Boogs77/BO6502_65C02-based_modular_computer/BO6502 BACKPLATE/README.md

Backplate
==============

Simple blackplate in two different versions. According to requirent 39 pins are used (Address, Data and Power&Signal) with 3 spare connection.

**backplate_final_rev02**

Backplate with 5v 7805 voltage regolator 

5 slots with 39 pins each
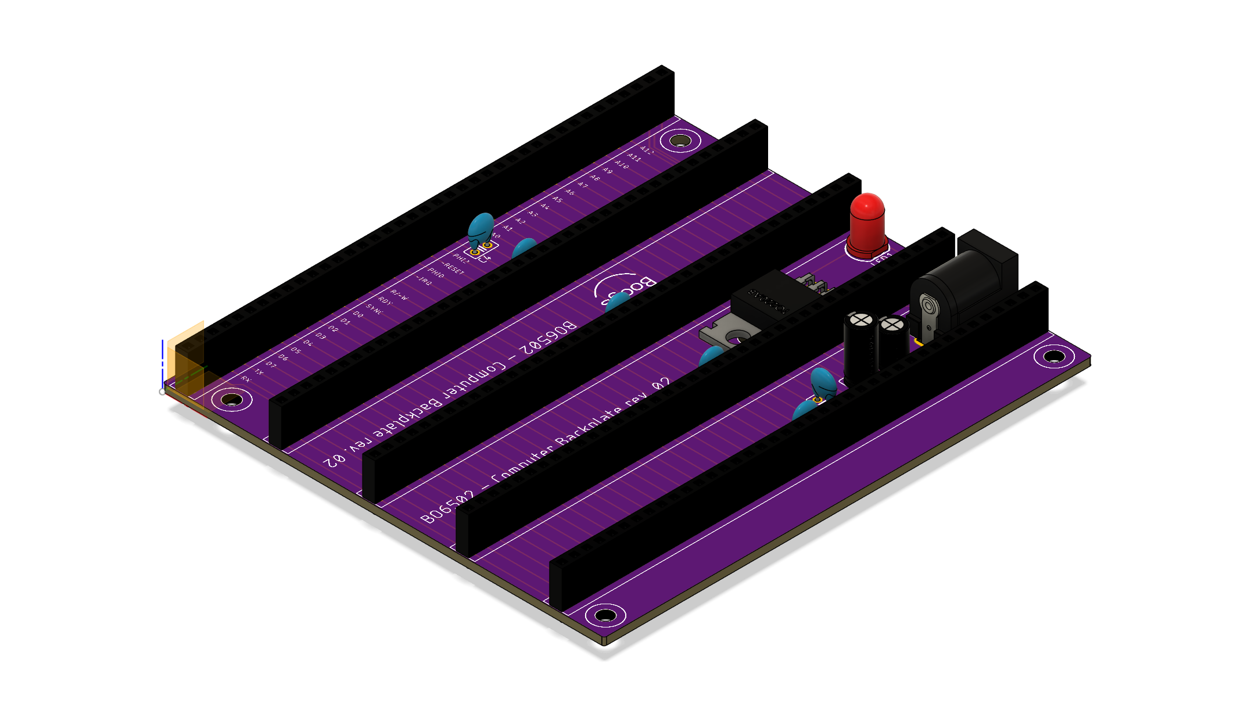
[picture p15: BO6502 BACKPLATE/gallery/backplate_final_rev02.png]


**backplate5V_final_rev01**

Backplate for 5v source  

5 slots with 39 pins each

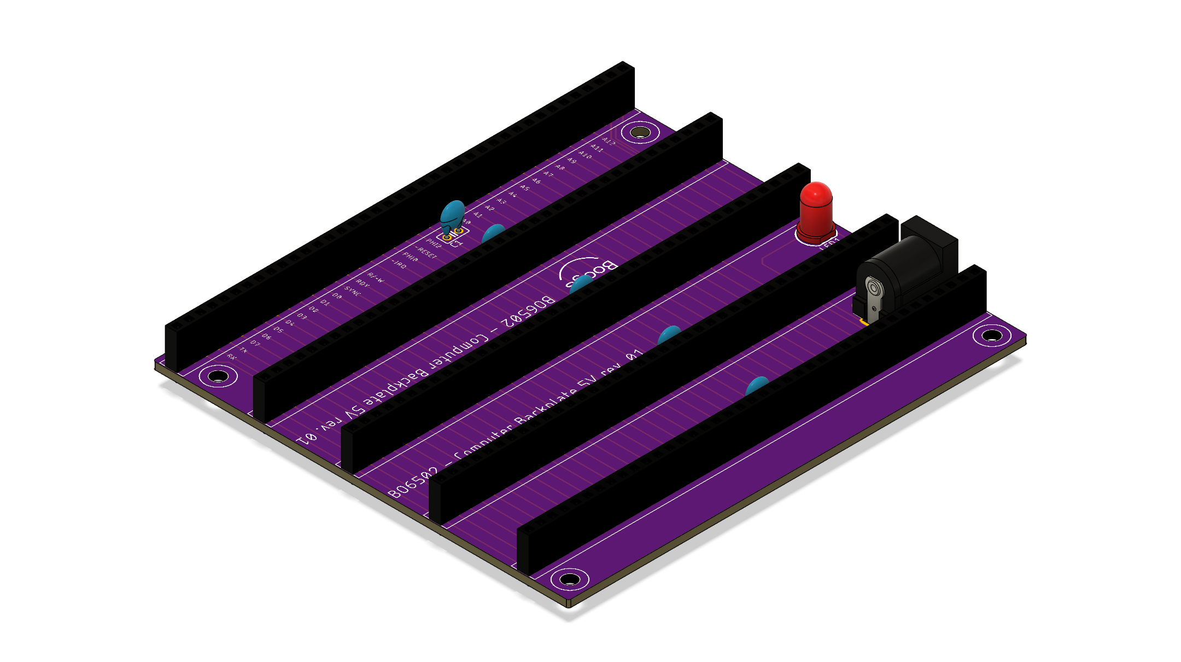
[picture p16: BO6502 BACKPLATE/gallery/backplate5V_final_rev01.png]
