Boogs77/BO6502_65C02-based_modular_computer/BO6502 CPU/eagle/CPU_final_rev02.brd

## EAGLE design BO6502 CPU/eagle/CPU_final_rev02.brd (2026-02-01)

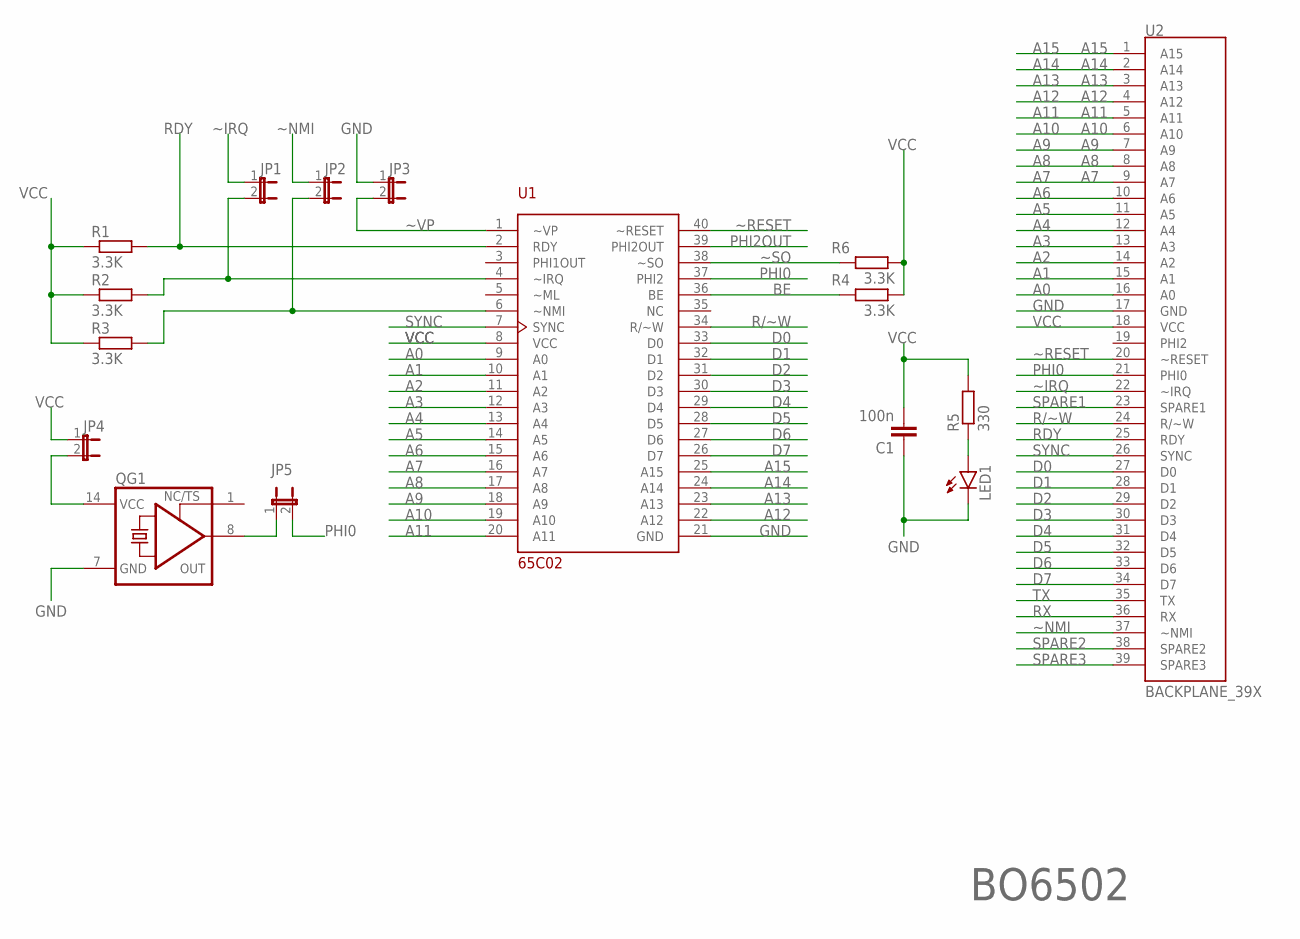
[picture p50: schematic CPU_final_rev02.sch]

Parts:
C1: 100n; C025-025X050
JP1, JP2, JP3, JP4, JP5: JP1E; JP1
LED1: LED5MM
QG1: XO-14; DIL14S
R1, R2, R3, R4, R6: 3.3K; 0207/10
R5: 330; 0207/10
U1: 65C02; DIL40
U2: BACKPLANE_39X; BP_39X

Connections:
A0: U1.9 (A0), U2.16 (A0)
A1: U1.10 (A1), U2.15 (A1)
A2: U1.11 (A2), U2.14 (A2)
A3: U1.12 (A3), U2.13 (A3)
A4: U1.13 (A4), U2.12 (A4)
A5: U1.14 (A5), U2.11 (A5)
A6: U1.15 (A6), U2.10 (A6)
A7: U1.16 (A7), U2.9 (A7)
A8: U1.17 (A8), U2.8 (A8)
A9: U1.18 (A9), U2.7 (A9)
A10: U1.19 (A10), U2.6 (A10)
A11: U1.20 (A11), U2.5 (A11)
A12: U1.22 (A12), U2.4 (A12)
A13: U1.23 (A13), U2.3 (A13)
A14: U1.24 (A14), U2.2 (A14)
A15: U1.25 (A15), U2.1 (A15)
BE: R4.1, U1.36 (BE)
D0: U1.33 (D0), U2.27 (D0)
D1: U1.32 (D1), U2.28 (D1)
D2: U1.31 (D2), U2.29 (D2)
D3: U1.30 (D3), U2.30 (D3)
D4: U1.29 (D4), U2.31 (D4)
D5: U1.28 (D5), U2.32 (D5)
D6: U1.27 (D6), U2.33 (D6)
D7: U1.26 (D7), U2.34 (D7)
GND: C1.1, JP3.1, LED1.K (C), QG1.7 (GND), U1.21 (GND), U2.17 (GND)
unnamed: JP4.2, QG1.14 (VCC)
unnamed: JP1.2, R2.2, U1.4 (~IRQ)
unnamed: JP2.2, R3.2, U1.6 (~NMI)
unnamed: JP5.1, QG1.8 (OUT)
unnamed: LED1.A, R5.1
PHI0: JP5.2, U1.37 (PHI2), U2.21 (PHI0)
PHI2OUT: U1.39 (PHI2OUT)
R/~W: U1.34 (R/~W), U2.24 (R/~W)
RDY: R1.2, U1.2 (RDY), U2.25 (RDY)
RX: U2.36 (RX)
SPARE1: U2.23 (SPARE1)
SPARE2: U2.38 (SPARE2)
SPARE3: U2.39 (SPARE3)
SYNC: U1.7 (SYNC), U2.26 (SYNC)
TX: U2.35 (TX)
VCC: C1.2, JP4.1, R1.1, R2.1, R3.1, R4.2, R5.2, R6.2, U1.8 (VCC), U2.18 (VCC)
~IRQ: JP1.1, U2.22 (~IRQ)
~NMI: JP2.1, U2.37 (~NMI)
~RESET: U1.40 (~RESET), U2.20 (~RESET)
~SO: R6.1, U1.38 (~SO)
~VP: JP3.2, U1.1 (~VP)

Notes on the sheet:
BO6502

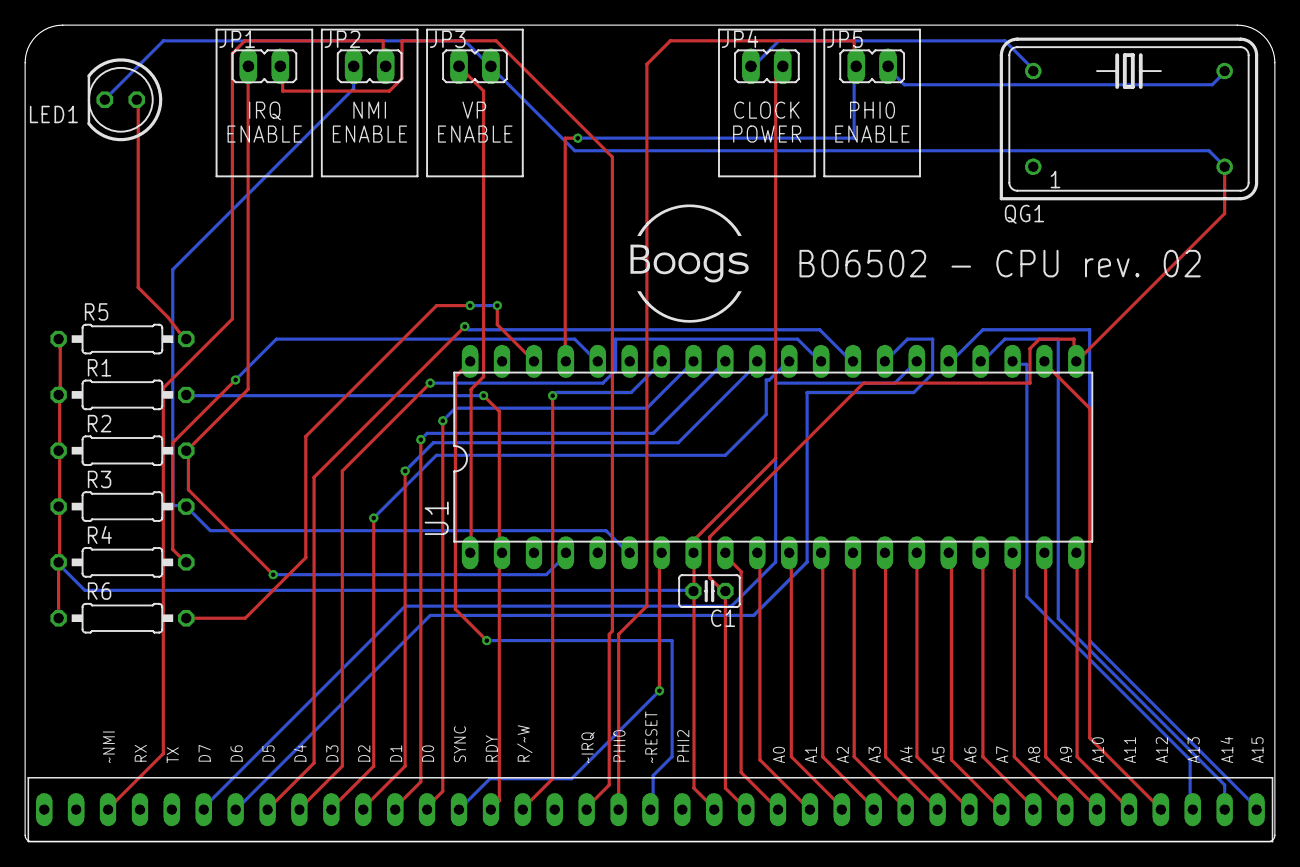
[picture p51: board CPU_final_rev02.brd from above]

Board: 2 copper layers, 99.5 x 65.0 mm, 16 parts (0 on the bottom side), 41 nets.
