Boogs77/BO6502_65C02-based_modular_computer/BO6502 CONNECTOR/eagle/connector_final_rev01.brd

## EAGLE design BO6502 CONNECTOR/eagle/connector_final_rev01.brd (2026-01-31)

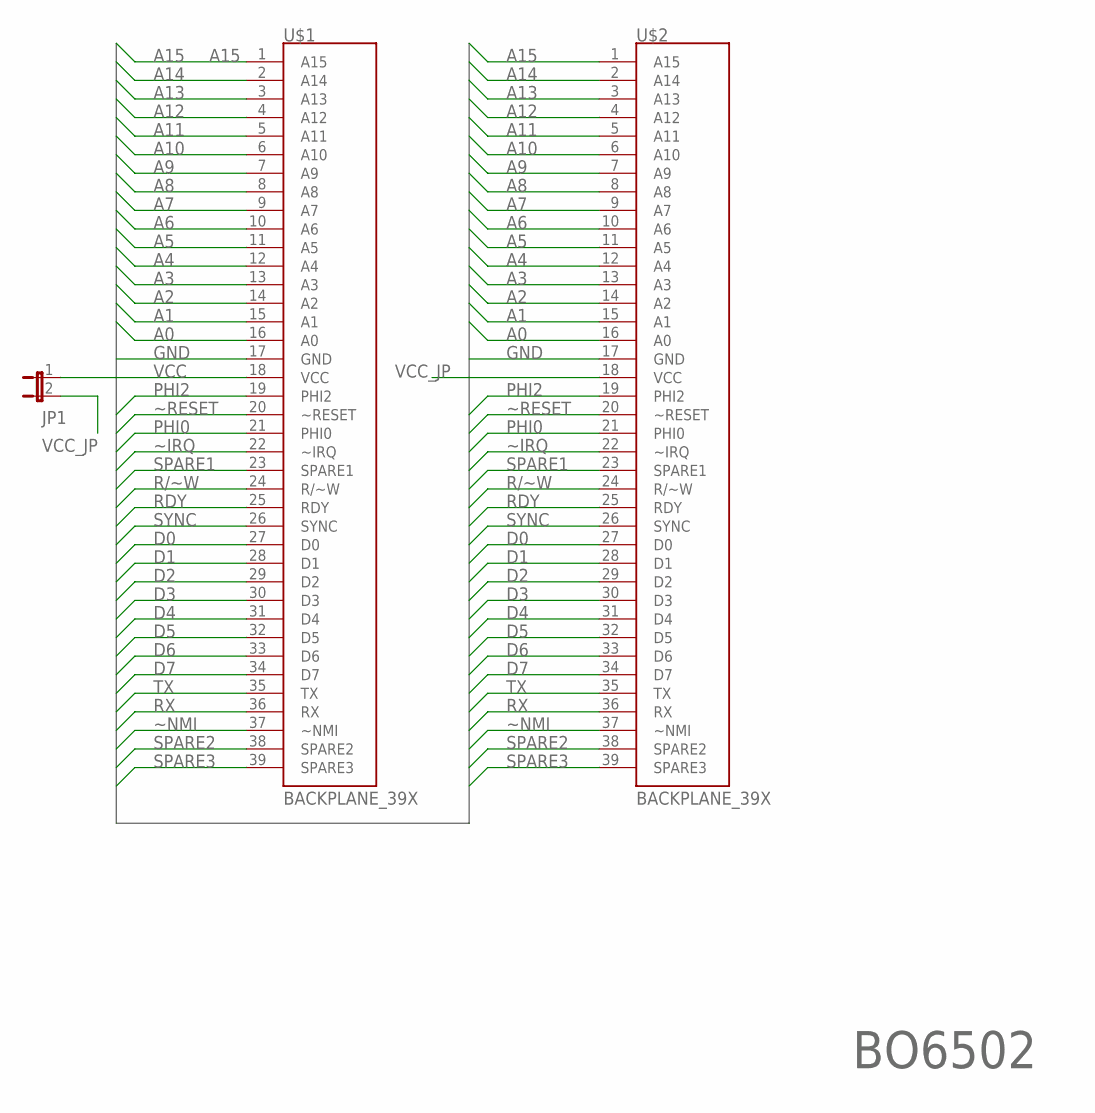
[picture p52: schematic connector_final_rev01.sch]

Parts:
JP1: JP1E; JP1
U$1, U$2: BACKPLANE_39X; BP_39X

Connections:
A0: U$1.16 (A0), U$2.16 (A0)
A1: U$1.15 (A1), U$2.15 (A1)
A2: U$1.14 (A2), U$2.14 (A2)
A3: U$1.13 (A3), U$2.13 (A3)
A4: U$1.12 (A4), U$2.12 (A4)
A5: U$1.11 (A5), U$2.11 (A5)
A6: U$1.10 (A6), U$2.10 (A6)
A7: U$1.9 (A7), U$2.9 (A7)
A8: U$1.8 (A8), U$2.8 (A8)
A9: U$1.7 (A9), U$2.7 (A9)
A10: U$1.6 (A10), U$2.6 (A10)
A11: U$1.5 (A11), U$2.5 (A11)
A12: U$1.4 (A12), U$2.4 (A12)
A13: U$1.3 (A13), U$2.3 (A13)
A14: U$1.2 (A14), U$2.2 (A14)
A15: U$1.1 (A15), U$2.1 (A15)
D0: U$1.27 (D0), U$2.27 (D0)
D1: U$1.28 (D1), U$2.28 (D1)
D2: U$1.29 (D2), U$2.29 (D2)
D3: U$1.30 (D3), U$2.30 (D3)
D4: U$1.31 (D4), U$2.31 (D4)
D5: U$1.32 (D5), U$2.32 (D5)
D6: U$1.33 (D6), U$2.33 (D6)
D7: U$1.34 (D7), U$2.34 (D7)
GND: U$1.17 (GND), U$2.17 (GND)
PHI0: U$1.21 (PHI0), U$2.21 (PHI0)
PHI2: U$1.19 (PHI2), U$2.19 (PHI2)
R/~W: U$1.24 (R/~W), U$2.24 (R/~W)
RDY: U$1.25 (RDY), U$2.25 (RDY)
RX: U$1.36 (RX), U$2.36 (RX)
SPARE1: U$1.23 (SPARE1), U$2.23 (SPARE1)
SPARE2: U$1.38 (SPARE2), U$2.38 (SPARE2)
SPARE3: U$1.39 (SPARE3), U$2.39 (SPARE3)
SYNC: U$1.26 (SYNC), U$2.26 (SYNC)
TX: U$1.35 (TX), U$2.35 (TX)
VCC: JP1.1, U$1.18 (VCC)
VCC_JP: JP1.2, U$2.18 (VCC)
~IRQ: U$1.22 (~IRQ), U$2.22 (~IRQ)
~NMI: U$1.37 (~NMI), U$2.37 (~NMI)
~RESET: U$1.20 (~RESET), U$2.20 (~RESET)

Notes on the sheet:
BO6502

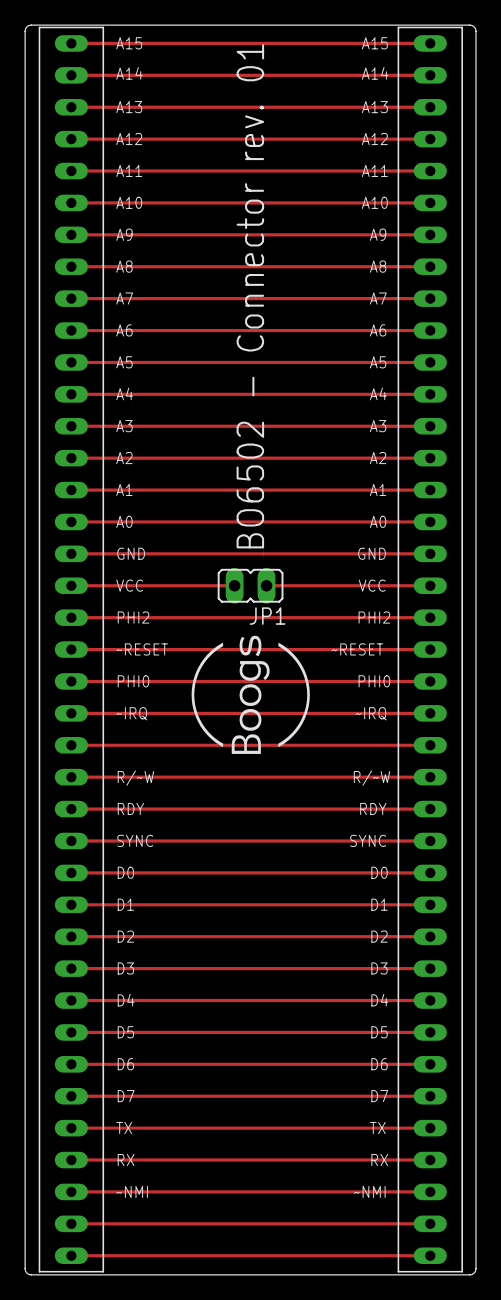
[picture p53: board connector_final_rev01.brd from above]

Board: 2 copper layers, 35.9 x 99.5 mm, 3 parts (0 on the bottom side), 40 nets.
