Boogs77/BO6502_65C02-based_modular_computer/BO6502 BACKPLATE/eagle/backplate5V_final_rev01.brd

## EAGLE design BO6502 BACKPLATE/eagle/backplate5V_final_rev01.brd (2026-01-31)

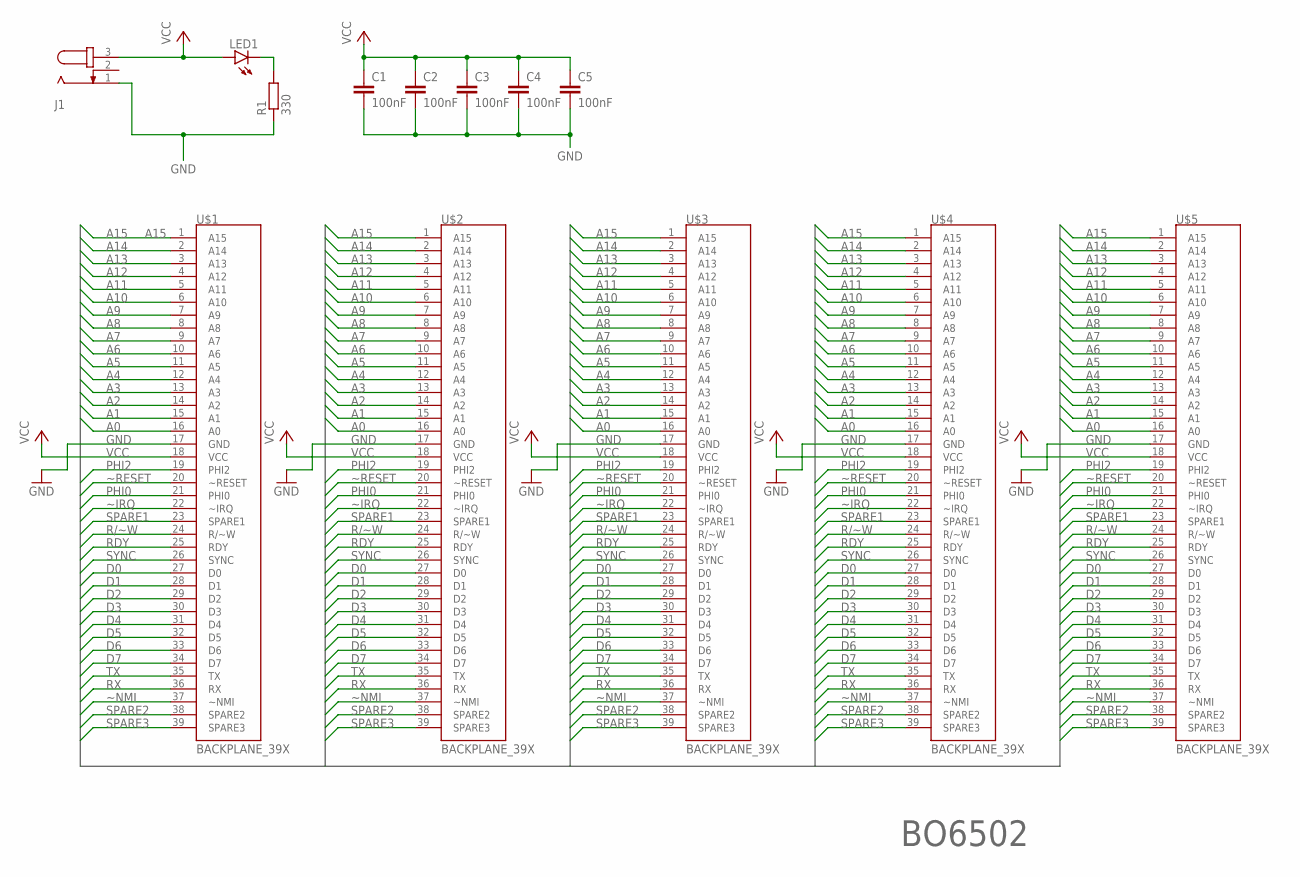
[picture p54: schematic backplate5V_final_rev01.sch]

Parts:
C1, C2, C3, C4, C5: 100nF; C025-025X050
J1: JACK-PLUG1; SPC4078
LED1: LED5MM
R1: 330; 0207/10
U$1, U$2, U$3, U$4, U$5: BACKPLANE_39X; BP_39X

Connections:
A0: U$1.16 (A0), U$2.16 (A0), U$3.16 (A0), U$4.16 (A0), U$5.16 (A0)
A1: U$1.15 (A1), U$2.15 (A1), U$3.15 (A1), U$4.15 (A1), U$5.15 (A1)
A2: U$1.14 (A2), U$2.14 (A2), U$3.14 (A2), U$4.14 (A2), U$5.14 (A2)
A3: U$1.13 (A3), U$2.13 (A3), U$3.13 (A3), U$4.13 (A3), U$5.13 (A3)
A4: U$1.12 (A4), U$2.12 (A4), U$3.12 (A4), U$4.12 (A4), U$5.12 (A4)
A5: U$1.11 (A5), U$2.11 (A5), U$3.11 (A5), U$4.11 (A5), U$5.11 (A5)
A6: U$1.10 (A6), U$2.10 (A6), U$3.10 (A6), U$4.10 (A6), U$5.10 (A6)
A7: U$1.9 (A7), U$2.9 (A7), U$3.9 (A7), U$4.9 (A7), U$5.9 (A7)
A8: U$1.8 (A8), U$2.8 (A8), U$3.8 (A8), U$4.8 (A8), U$5.8 (A8)
A9: U$1.7 (A9), U$2.7 (A9), U$3.7 (A9), U$4.7 (A9), U$5.7 (A9)
A10: U$1.6 (A10), U$2.6 (A10), U$3.6 (A10), U$4.6 (A10), U$5.6 (A10)
A11: U$1.5 (A11), U$2.5 (A11), U$3.5 (A11), U$4.5 (A11), U$5.5 (A11)
A12: U$1.4 (A12), U$2.4 (A12), U$3.4 (A12), U$4.4 (A12), U$5.4 (A12)
A13: U$1.3 (A13), U$2.3 (A13), U$3.3 (A13), U$4.3 (A13), U$5.3 (A13)
A14: U$1.2 (A14), U$2.2 (A14), U$3.2 (A14), U$4.2 (A14), U$5.2 (A14)
A15: U$1.1 (A15), U$2.1 (A15), U$3.1 (A15), U$4.1 (A15), U$5.1 (A15)
D0: U$1.27 (D0), U$2.27 (D0), U$3.27 (D0), U$4.27 (D0), U$5.27 (D0)
D1: U$1.28 (D1), U$2.28 (D1), U$3.28 (D1), U$4.28 (D1), U$5.28 (D1)
D2: U$1.29 (D2), U$2.29 (D2), U$3.29 (D2), U$4.29 (D2), U$5.29 (D2)
D3: U$1.30 (D3), U$2.30 (D3), U$3.30 (D3), U$4.30 (D3), U$5.30 (D3)
D4: U$1.31 (D4), U$2.31 (D4), U$3.31 (D4), U$4.31 (D4), U$5.31 (D4)
D5: U$1.32 (D5), U$2.32 (D5), U$3.32 (D5), U$4.32 (D5), U$5.32 (D5)
D6: U$1.33 (D6), U$2.33 (D6), U$3.33 (D6), U$4.33 (D6), U$5.33 (D6)
D7: U$1.34 (D7), U$2.34 (D7), U$3.34 (D7), U$4.34 (D7), U$5.34 (D7)
GND: C1.2, C2.2, C3.2, C4.2, C5.2, J1.1, R1.1, U$1.17 (GND), U$2.17 (GND), U$3.17 (GND), U$4.17 (GND), U$5.17 (GND)
unnamed: LED1.K (C), R1.2
PHI0: U$1.21 (PHI0), U$2.21 (PHI0), U$3.21 (PHI0), U$4.21 (PHI0), U$5.21 (PHI0)
PHI2: U$1.19 (PHI2), U$2.19 (PHI2), U$3.19 (PHI2), U$4.19 (PHI2), U$5.19 (PHI2)
R/~W: U$1.24 (R/~W), U$2.24 (R/~W), U$3.24 (R/~W), U$4.24 (R/~W), U$5.24 (R/~W)
RDY: U$1.25 (RDY), U$2.25 (RDY), U$3.25 (RDY), U$4.25 (RDY), U$5.25 (RDY)
RX: U$1.36 (RX), U$2.36 (RX), U$3.36 (RX), U$4.36 (RX), U$5.36 (RX)
SPARE1: U$1.23 (SPARE1), U$2.23 (SPARE1), U$3.23 (SPARE1), U$4.23 (SPARE1), U$5.23 (SPARE1)
SPARE2: U$1.38 (SPARE2), U$2.38 (SPARE2), U$3.38 (SPARE2), U$4.38 (SPARE2), U$5.38 (SPARE2)
SPARE3: U$1.39 (SPARE3), U$2.39 (SPARE3), U$3.39 (SPARE3), U$4.39 (SPARE3), U$5.39 (SPARE3)
SYNC: U$1.26 (SYNC), U$2.26 (SYNC), U$3.26 (SYNC), U$4.26 (SYNC), U$5.26 (SYNC)
TX: U$1.35 (TX), U$2.35 (TX), U$3.35 (TX), U$4.35 (TX), U$5.35 (TX)
VCC: C1.1, C2.1, C3.1, C4.1, C5.1, J1.3, LED1.A, U$1.18 (VCC), U$2.18 (VCC), U$3.18 (VCC), U$4.18 (VCC), U$5.18 (VCC)
~IRQ: U$1.22 (~IRQ), U$2.22 (~IRQ), U$3.22 (~IRQ), U$4.22 (~IRQ), U$5.22 (~IRQ)
~NMI: U$1.37 (~NMI), U$2.37 (~NMI), U$3.37 (~NMI), U$4.37 (~NMI), U$5.37 (~NMI)
~RESET: U$1.20 (~RESET), U$2.20 (~RESET), U$3.20 (~RESET), U$4.20 (~RESET), U$5.20 (~RESET)

Notes on the sheet:
BO6502

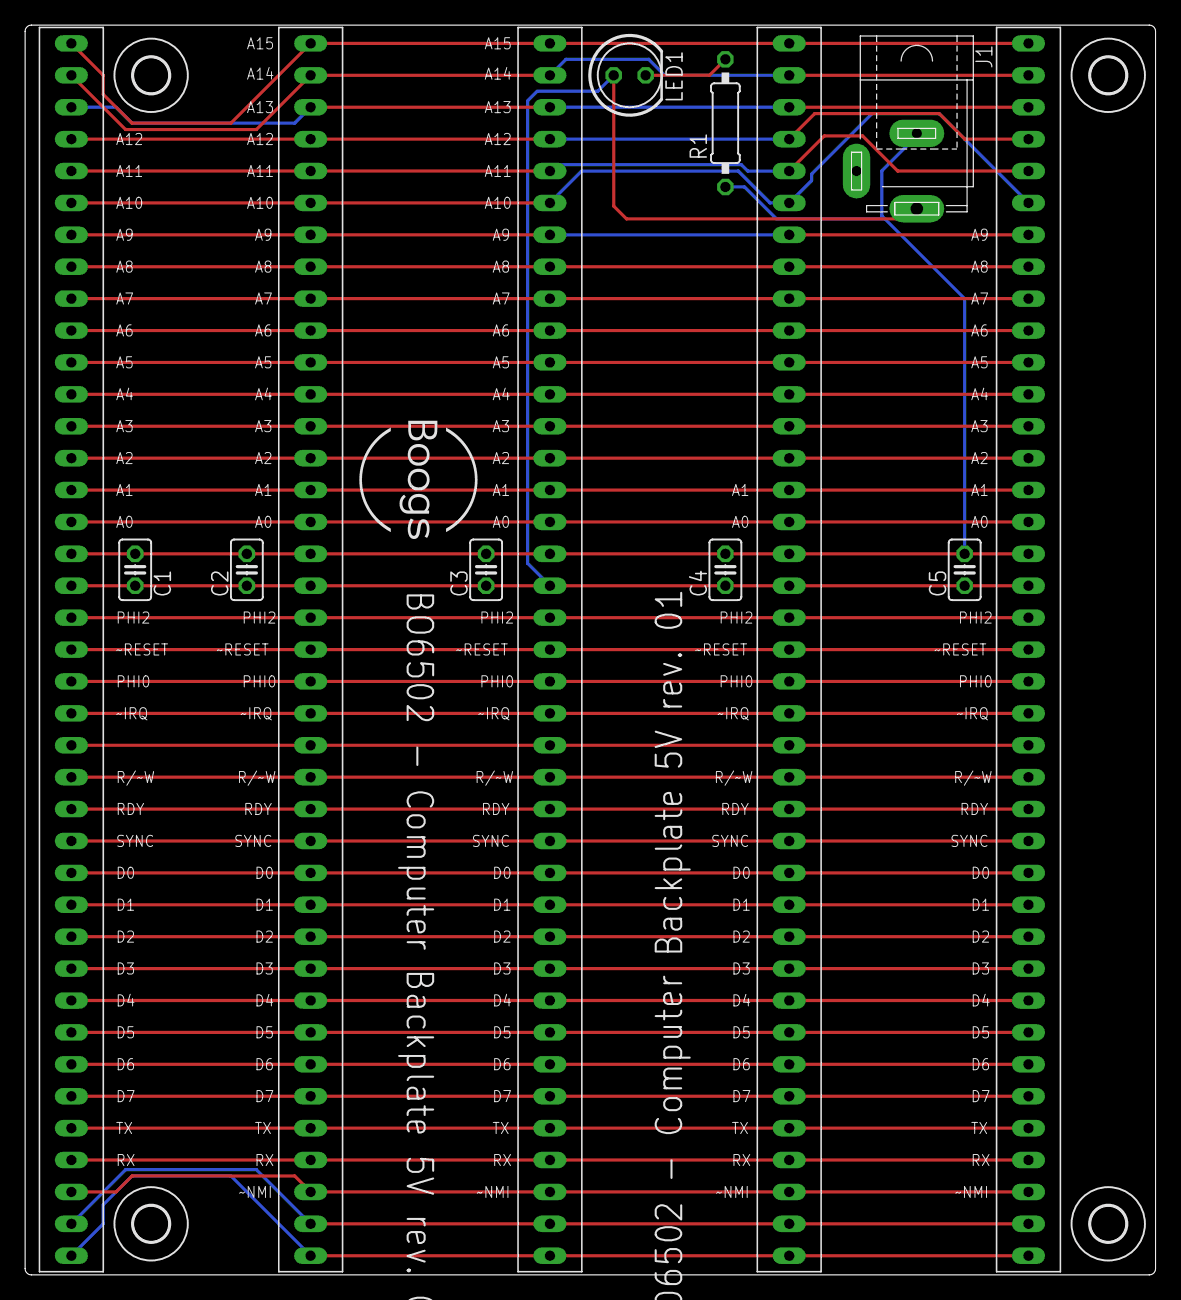
[picture p55: board backplate5V_final_rev01.brd from above]

Board: 2 copper layers, 90.0 x 99.5 mm, 17 parts (0 on the bottom side), 40 nets.

Other parts of the board:
U$7, U$8, U$9, U$10: 2,8
